LyndLabs/DNS-DriveBy/tests/scripts/data/log10.csv

WigleWifi-1.4 | appRelease=2.53 | model=D1-Mini-Pro | release=0.0.0 | device=NetDash | display=SSD1306 | board=ESP8266 | brand=Wemos
MAC | SSID | AuthMode | FirstSeen | Channel | RSSI | CurrentLatitude | CurrentLongitude | AltitudeMeters | AccuracyMeters | Type
B0:E4:D5:0D:CD:2A | WCGWIFI | [WPA2-PSK-CCMP+TKIP][ESS] | 2023-3-5 2:59:25 | 1 | -82 | 33.885585 | -118.029156 | 18.8 | 68 | WIFI
34:97:F6:20:CE:48 | SOCAL | [WPA2-PSK-CCMP+TKIP][ESS] | 2023-3-5 2:59:25 | 1 | -83 | 33.885585 | -118.029156 | 18.8 | 68 | WIFI
A8:9A:93:C9:BF:E6 | MySpectrumWiFi48-2G | [WPA2-PSK-CCMP+TKIP][ESS] | 2023-3-5 2:59:25 | 1 | -87 | 33.885585 | -118.029156 | 18.8 | 68 | WIFI
CC:40:D0:9E:07:DC | NETGEAR61 | [WPA2-PSK-CCMP+TKIP][ESS] | 2023-3-5 2:59:25 | 1 | -86 | 33.885585 | -118.029156 | 18.8 | 68 | WIFI
7C:DB:98:A1:16:A1 | MySpectrumWiFiA3-2G | [WPA2-PSK-CCMP+TKIP][ESS] | 2023-3-5 2:59:25 | 1 | -81 | 33.885585 | -118.029156 | 18.8 | 68 | WIFI
D8:38:FC:89:35:68 | DWW-SDI | [WPA2-PSK-CCMP+TKIP][ESS] | 2023-3-5 2:59:25 | 1 | -84 | 33.885585 | -118.029156 | 18.8 | 68 | WIFI
D8:38:FC:C9:35:68 | DWW-SFS | [WEP][ESS] | 2023-3-5 2:59:25 | 1 | -84 | 33.885585 | -118.029156 | 18.8 | 68 | WIFI
D8:38:FC:09:35:69 | DWW-BC | [WEP][ESS] | 2023-3-5 2:59:25 | 1 | -84 | 33.885585 | -118.029156 | 18.8 | 68 | WIFI
D8:38:FC:49:35:69 | DWW-Guest-Wifi | [WPA2-PSK-CCMP+TKIP][ESS] | 2023-3-5 2:59:25 | 1 | -84 | 33.885585 | -118.029156 | 18.8 | 68 | WIFI
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
D8:38:FC:49:1F:69 | DWW-Guest-Wifi | [WPA2-PSK-CCMP+TKIP][ESS] | 2023-3-5 2:59:25 | 11 | -88 | 33.885585 | -118.029156 | 18.8 | 68 | WIFI
98:1E:19:53:29:76 | SEEDUSA-2G | [WPA2-PSK-CCMP+TKIP][ESS] | 2023-3-5 2:59:25 | 1 | -86 | 33.885585 | -118.029156 | 18.8 | 68 | WIFI
