LyndLabs/DNS-DriveBy/src/Demo/graphics.h

#ifndef FONT_DEJAVU_SANS_MONO_10
#define FONT_DEJAVU_SANS_MONO_10

// Created by http://oleddisplay.squix.ch/ Consider a donation
const uint8_t DejaVu_Sans_Mono_10[] PROGMEM = {
  0x06, // Width: 6
  0x0D, // Height: 13
  0x20, // First Char: 32
  0xE0, // Numbers of Chars: 224

  // Jump Table:
  0xFF, 0xFF, 0x00, 0x06,  // 32:65535
  0x00, 0x00, 0x08, 0x06,  // 33:0
  0x00, 0x08, 0x09, 0x06,  // 34:8
  0x00, 0x11, 0x0B, 0x06,  // 35:17
  0x00, 0x1C, 0x0C, 0x06,  // 36:28
  0x00, 0x28, 0x0C, 0x06,  // 37:40
  0x00, 0x34, 0x0C, 0x06,  // 38:52
  0x00, 0x40, 0x07, 0x06,  // 39:64
  0x00, 0x47, 0x08, 0x06,  // 40:71
  0x00, 0x4F, 0x08, 0x06,  // 41:79
  0x00, 0x57, 0x0B, 0x06,  // 42:87
  0x00, 0x62, 0x0B, 0x06,  // 43:98
  0x00, 0x6D, 0x06, 0x06,  // 44:109
  0x00, 0x73, 0x09, 0x06,  // 45:115
  0x00, 0x7C, 0x06, 0x06,  // 46:124
  0x00, 0x82, 0x0B, 0x06,  // 47:130
  0x00, 0x8D, 0x0C, 0x06,  // 48:141
  0x00, 0x99, 0x0C, 0x06,  // 49:153
  0x00, 0xA5, 0x0C, 0x06,  // 50:165
  0x00, 0xB1, 0x0C, 0x06,  // 51:177
  0x00, 0xBD, 0x0B, 0x06,  // 52:189
  0x00, 0xC8, 0x0C, 0x06,  // 53:200
  0x00, 0xD4, 0x0C, 0x06,  // 54:212
  0x00, 0xE0, 0x0B, 0x06,  // 55:224
  0x00, 0xEB, 0x0C, 0x06,  // 56:235
  0x00, 0xF7, 0x0C, 0x06,  // 57:247
  0x01, 0x03, 0x06, 0x06,  // 58:259
  0x01, 0x09, 0x06, 0x06,  // 59:265
  0x01, 0x0F, 0x0C, 0x06,  // 60:271
  0x01, 0x1B, 0x09, 0x06,  // 61:283
  0x01, 0x24, 0x0B, 0x06,  // 62:292
  0x01, 0x2F, 0x09, 0x06,  // 63:303
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
   0xdd, 0x9f, 0x83, 0x01, 0xc0, 0xc1, 0x39, 0x7f, 0x00, 0x0e, 0x38, 0x38,
   0x03, 0x66, 0x1c, 0xff, 0x1d, 0xb8, 0x83, 0x01, 0xc0, 0xc1, 0x39, 0x7e,
   0x00, 0x0e, 0x38, 0x38, 0x03, 0x66, 0x0e, 0xff, 0x1c, 0xb0, 0x83, 0x01,
   0xc0, 0xe1, 0x39, 0x7c, 0xfe, 0x0f, 0x38, 0x3c, 0x03, 0xe6, 0x07, 0x03,
   0x1c, 0xb0, 0xbf, 0x01, 0xc0, 0xff, 0x38, 0x78, 0xfe, 0x0f, 0xf8, 0x1f,
   0x03, 0xe6, 0x03, 0xff, 0xfc, 0x3f, 0xbf, 0x01, 0xc0, 0xff, 0x38, 0x70,
   0xfe, 0x07, 0xf8, 0x0f, 0x03, 0xe6, 0x01, 0x7f, 0xf8, 0x1f, 0xbe, 0x01,
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
